superrm11/VexDebugBoard_PCB/Pictures/PXL_20221127_214113786.jpg

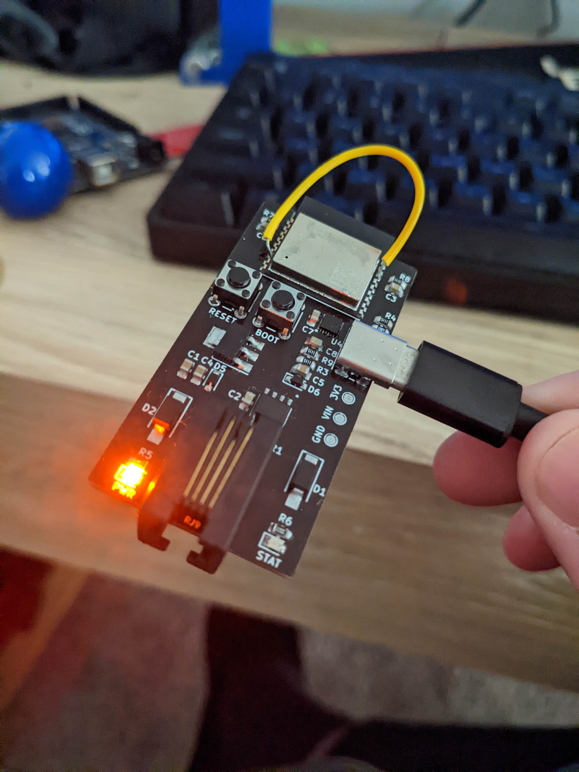
Pictures/PXL_20221127_214113786.jpg
