superrm11/VexDebugBoard_PCB/plot/Vex_Debug.jpg

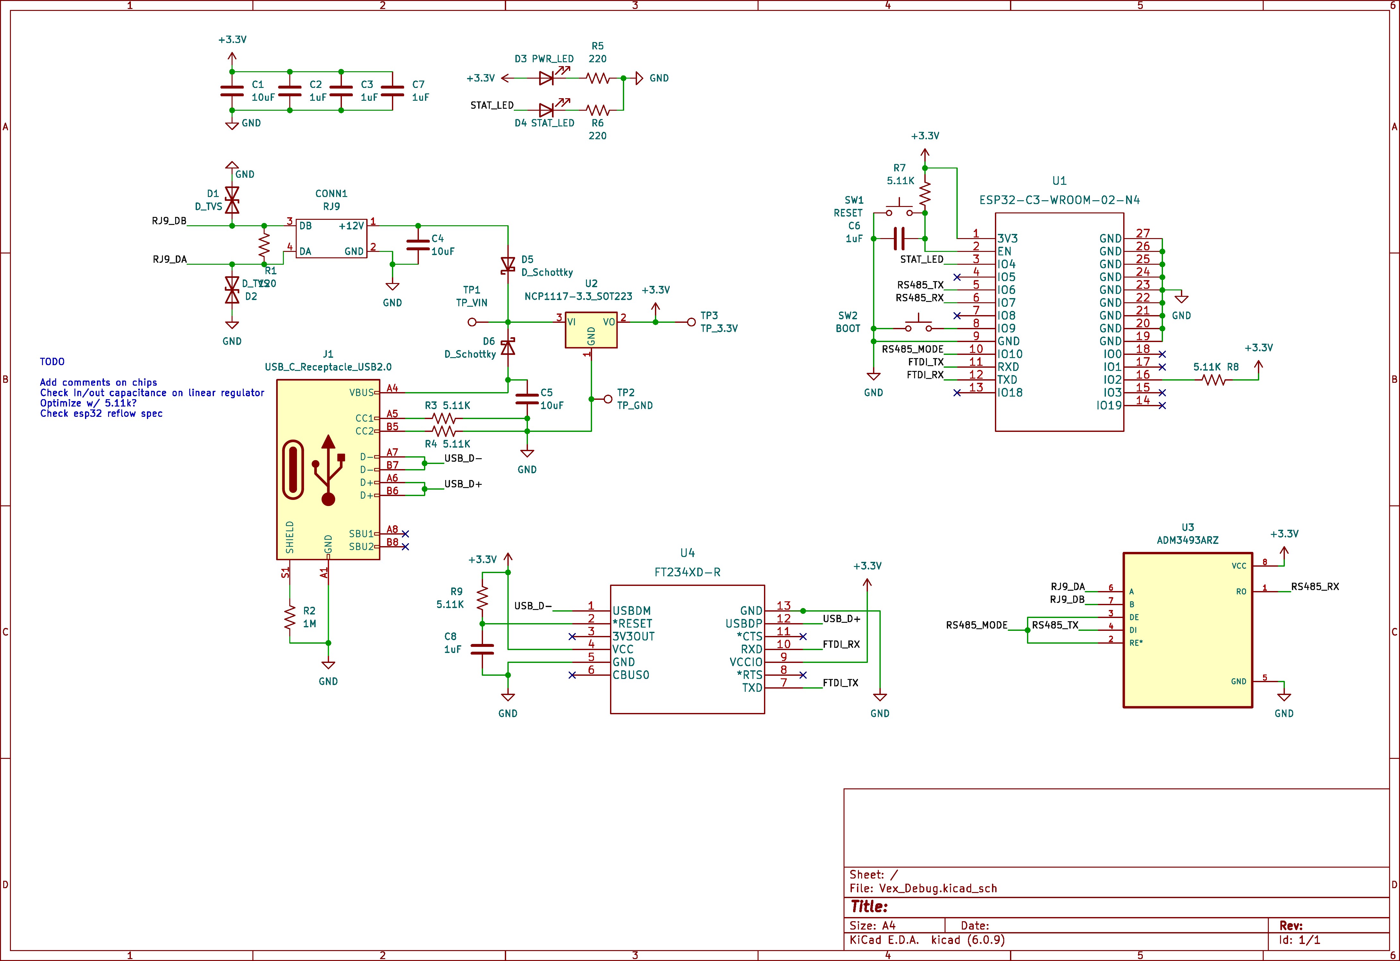
plot/Vex_Debug.jpg
