superrm11/VexDebugBoard_PCB/plot/Vex_Debug.png

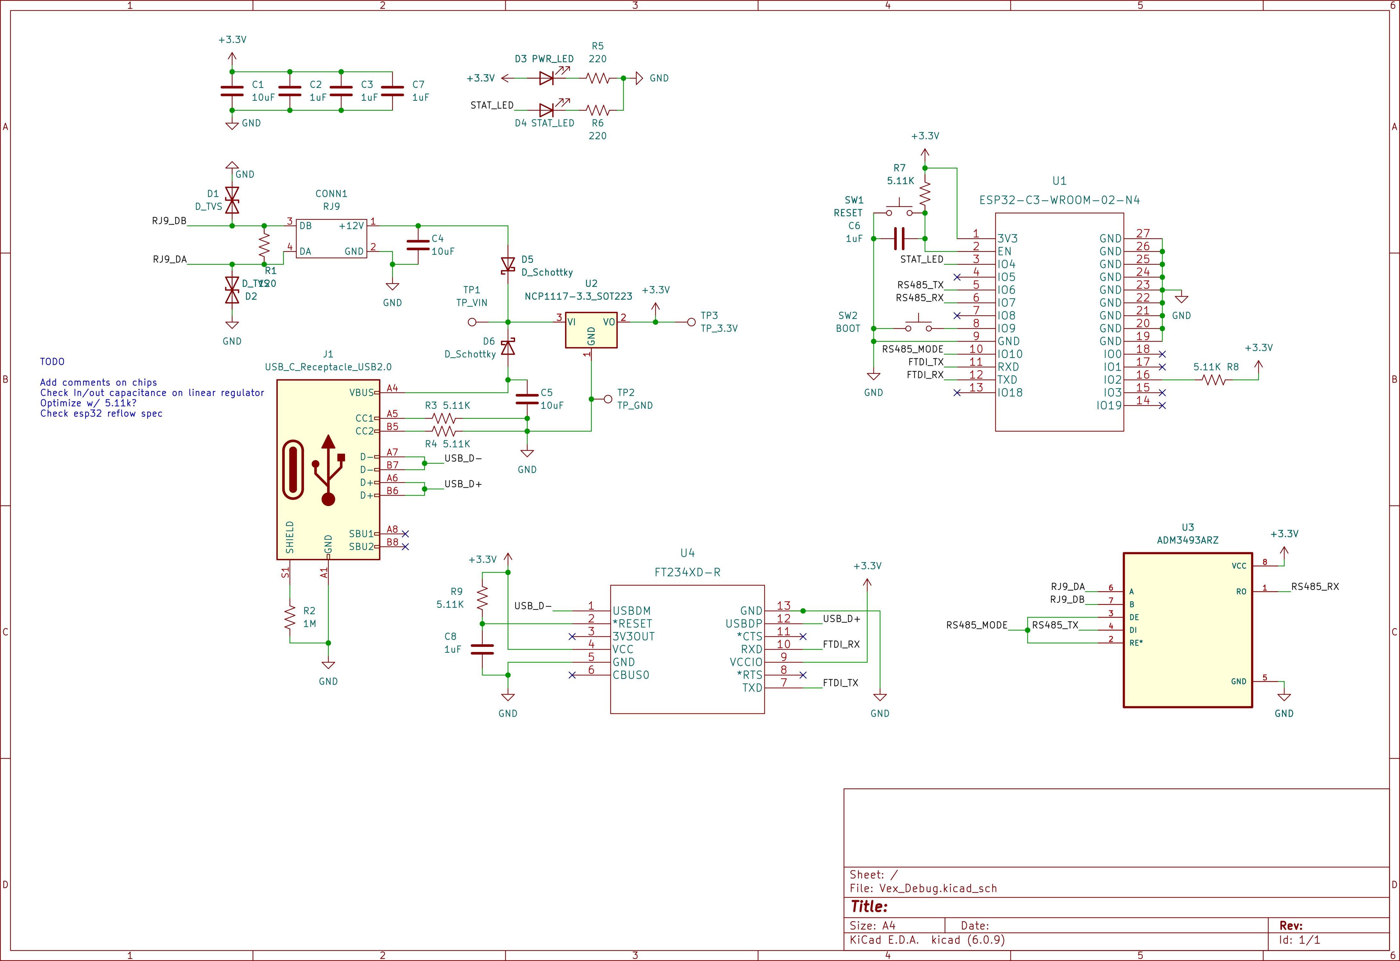
plot/Vex_Debug.png
